jgOhYeah/ArduinoIrrigationController/SlaveUnit/SlaveUnit3.7/notes.ino

/*
 * TODO: Flash leds - CURRENTLY IN THE MIDDLE OF IMPLEMENTING - ERRORS
 *    - When button is pressed to reset the baud rate in settings - lights sometime do not change / get stuck in the wrong pattern.
 * TODO: Set default baud to be 38400 instead of 9600
 * TODO: Debug mode?
 * TODO: Optimise strings so that they are stored in separate arrays and shared to save memory?
 * 
 * Slaves sometimes don't respond to requests for eeprom settings and appear as not connected
 * 
 * Slave sometimes does not send what state it is in.
 * 
 * bus id eeprom setting for slaves - i don't think it is possible
 */
