jgOhYeah/ArduinoIrrigationController/SlaveUnit/SlaveUnityFromScratch/defines.h

#define masterId 255
#define myId 44
#define reportStatus 's'
#define overwriteStatus 'w'
#define reset 'x'
#define setStatus 'r'
#define bayUnknown 0
#define bayShut 1
#define bayHalf 2
#define bayOpen 3
#define bayNotPresent 4

#define buttonPin 8
#define upLed 7
#define halfLed 6
#define downLed 5
#define motorA 2
#define motorB 3
char bayStatus = bayUnknown;
